med-lasers/Dosimeter_RadSens_NarodMon/Pictures/image 1.jpeg

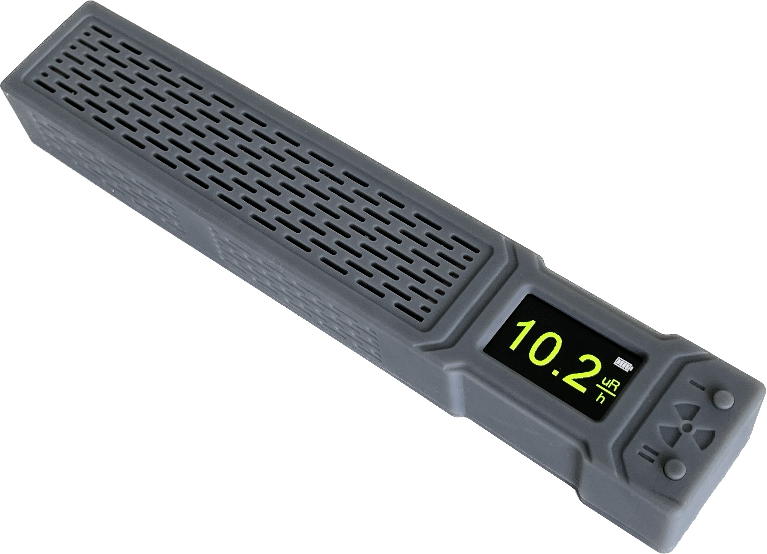
Pictures/image 1.jpeg
