med-lasers/Dosimeter_RadSens_NarodMon/Pictures/image 2.jpeg

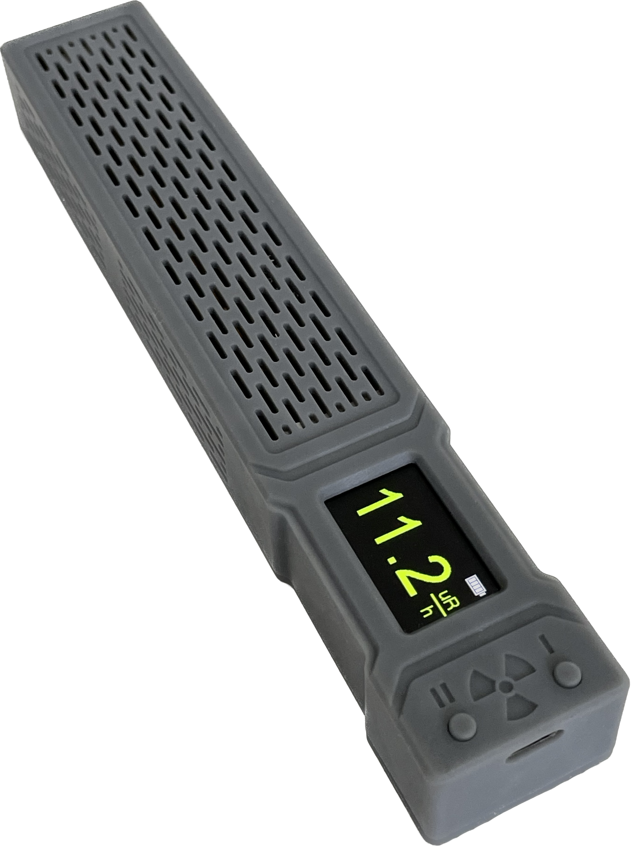
Pictures/image 2.jpeg
