med-lasers/Dosimeter_RadSens_NarodMon/Software/clipart.h

#define ICON_W 37
#define ICON_H 36
#define FRAME_COUT 1

#if defined(__AVR__)
  #include <avr/pgmspace.h>
#elif defined(__PIC32MX__)
  #define PROGMEM
#elif defined(__arm__)
  #define PROGMEM
#endif

extern const uint16_t clipart[] PROGMEM= {
0x0000,0x0000,0x0000,0x0000,0x0000,0x0000,0x0000,0x0000,0x0000,0x0000,0x0000,0x0000,0x0000,0x0000,0x4A20,0x83C0,0xACE0,0xC580,0xC5C0,0xBD80,0xACE0,0x83A0,0x41E0,0x0000,0x0000,0x0000,0x0000,0x0000,0x0000,0x0000,0x0000,0x0000,0x0000,0x0000,0x0000,0x0000,0x0000,
0x0000,0x0000,0x0000,0x0000,0x0000,0x0000,0x0000,0x0000,0x0000,0x0000,0x0000,0x7360,0xEEE0,0xFFE0,0xFFE0,0xFFC0,0xFFA0,0xFFA0,0xFFA0,0xFFC0,0xEEC0,0xFFE0,0xFFE0,0xFFE0,0xE680,0x62E0,0x0000,0x0000,0x0000,0x0000,0x0000,0x0000,0x0000,0x0000,0x0000,0x0000,0x0000,
0x0000,0x0000,0x0000,0x0000,0x0000,0x0000,0x0000,0x0000,0x0000,0x8C00,0xFFE0,0xFFE0,0xFF80,0xFF60,0xFF60,0xFF60,0xFF60,0xFF60,0xFF60,0xFFE0,0x4200,0x0000,0x18C0,0x9460,0xFFE0,0xFFE0,0xFFE0,0x7340,0x0000,0x0000,0x0000,0x0000,0x0000,0x0000,0x0000,0x0000,0x0000,
0x0000,0x0000,0x0000,0x0000,0x0000,0x0000,0x0000,0x2960,0xFFC0,0xFFE0,0xFF60,0xFF60,0xFF60,0xFF60,0xFF60,0xFF60,0xFF60,0xFF60,0xFF60,0xFFE0,0x20E0,0x0000,0x0000,0x0000,0x0000,0x5AA0,0xFF80,0xFFE0,0xFF40,0x0860,0x0000,0x0000,0x0000,0x0000,0x0000,0x0000,0x0000,
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
0x0000,0x0000,0x0000,0x0000,0x0000,0x0000,0x0000,0x0000,0x0000,0x0000,0x0000,0x0000,0x0000,0x0000,0x4A20,0x83C0,0xACE0,0xCDE0,0xD620,0xCDE0,0xB520,0x83E0,0x41E0,0x0000,0x0000,0x0000,0x0000,0x0000,0x0000,0x0000,0x0000,0x0000,0x0000,0x0000,0x0000,0x0000,0x0000
};
